olmoro/MKlon1/MKlon/Изображения/MKlon1full_bot.png

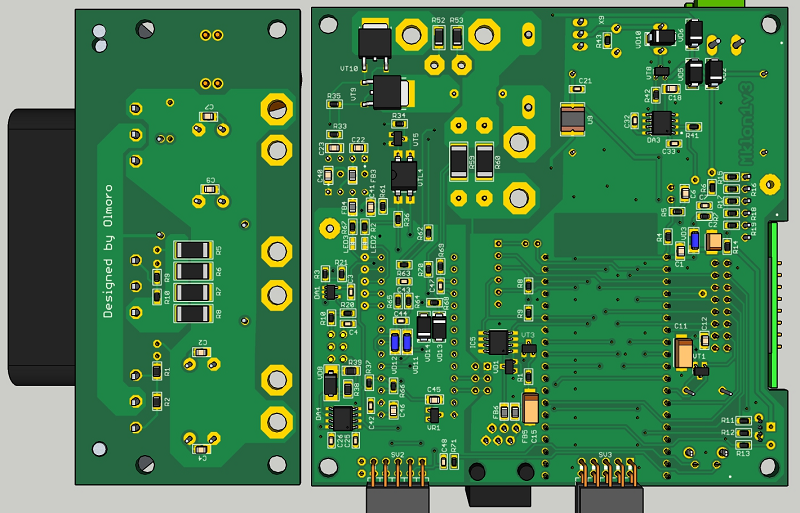
MKlon/Изображения/MKlon1full_bot.png
