olmoro/MKlon1/Модуль управления/Gerber/top.png

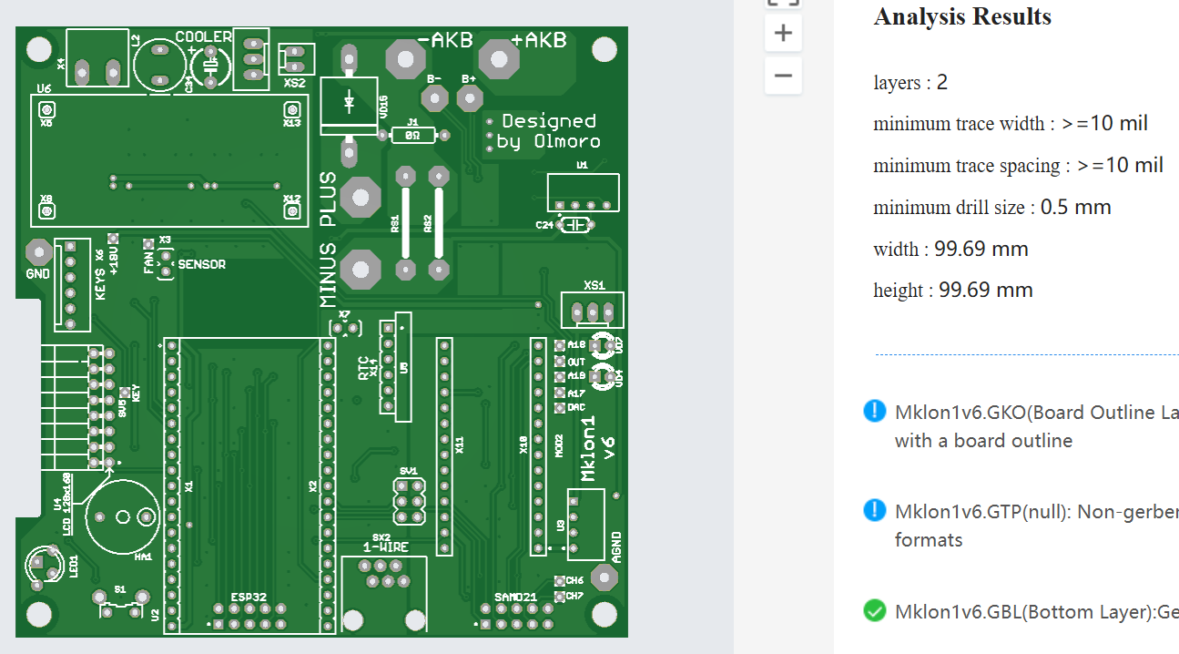
Модуль управления/Gerber/top.png
