olmoro/MKlon1/Модуль управления/Изображения/eagleUp_Mklon1v3_board_bottom.jpg

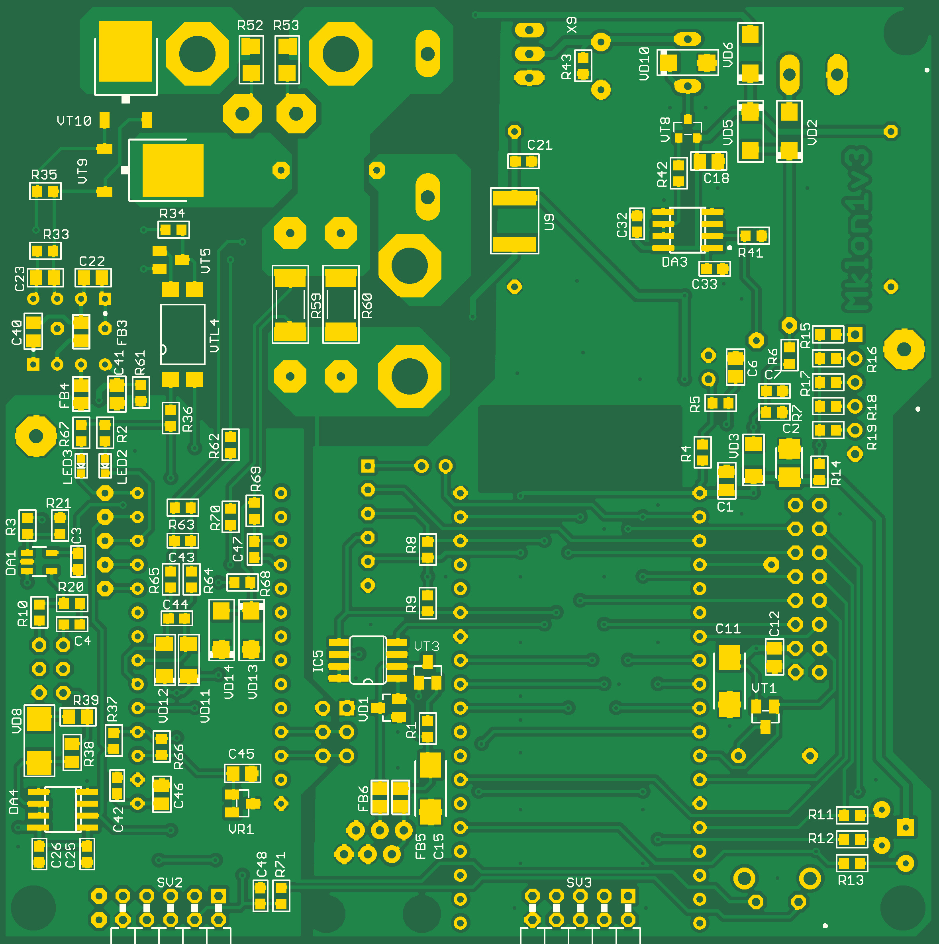
Модуль управления/Изображения/eagleUp_Mklon1v3_board_bottom.jpg
