olmoro/MKlon1/Модуль управления/Изображения/MKlon1v6_top.jpg

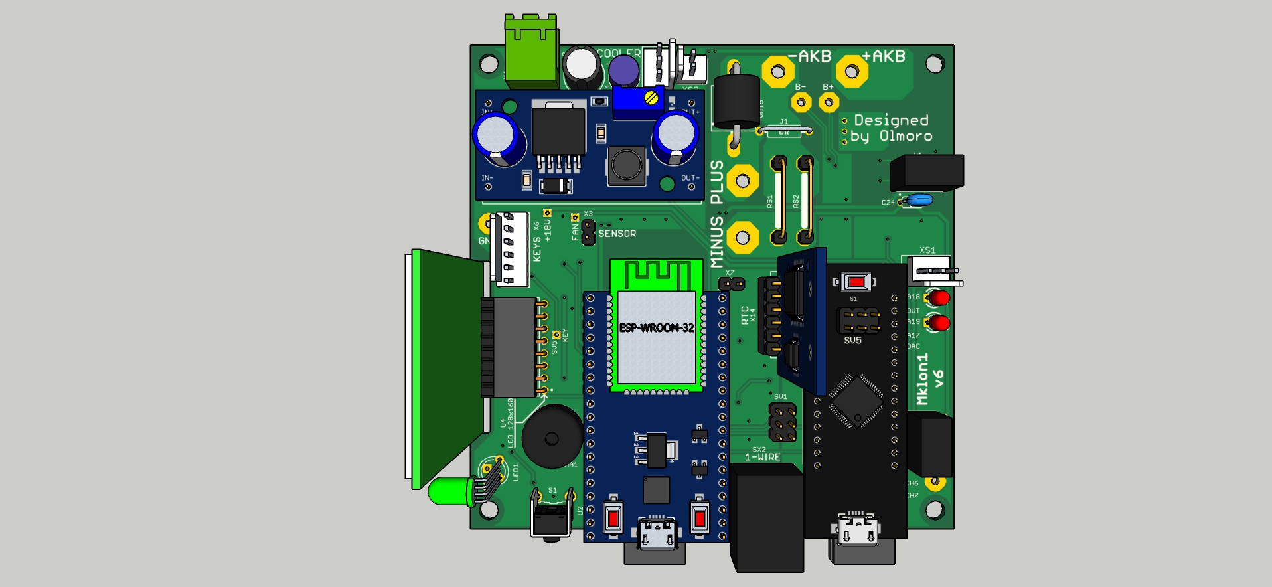
Модуль управления/Изображения/MKlon1v6_top.jpg
