olmoro/MKlon1/Силовой модуль/Изображения/MPmod.png

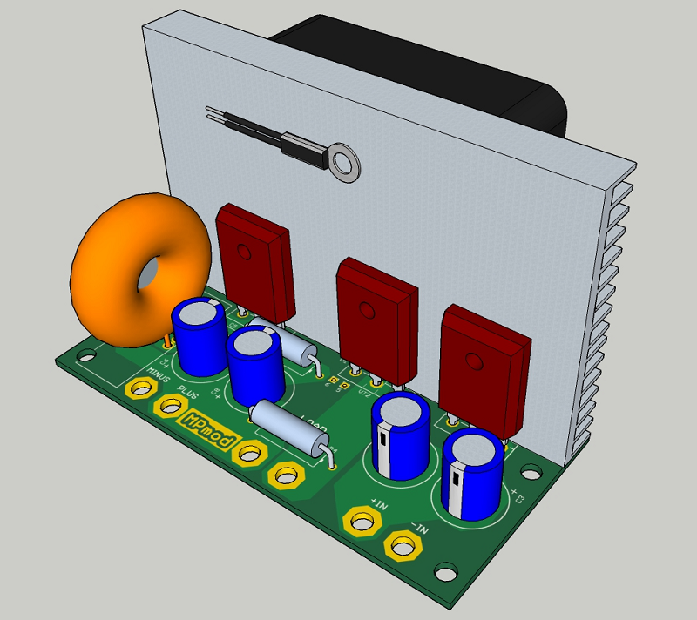
Силовой модуль/Изображения/MPmod.png
